stephanflug/digitales-Flugbuch/3D Druckerteile/Version 1 Basic mit Zero/DeckelV2.jpg

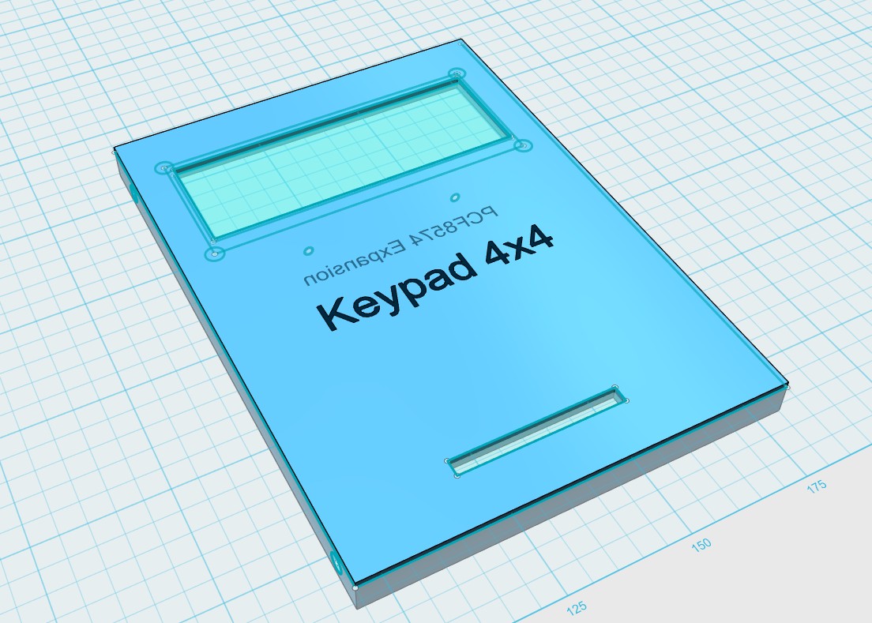
3D Druckerteile/Version 1 Basic mit Zero/DeckelV2.jpg
