stephanflug/digitales-Flugbuch/3D Druckerteile/Version 1 Basic mit Zero/GehäuseV2.jpg

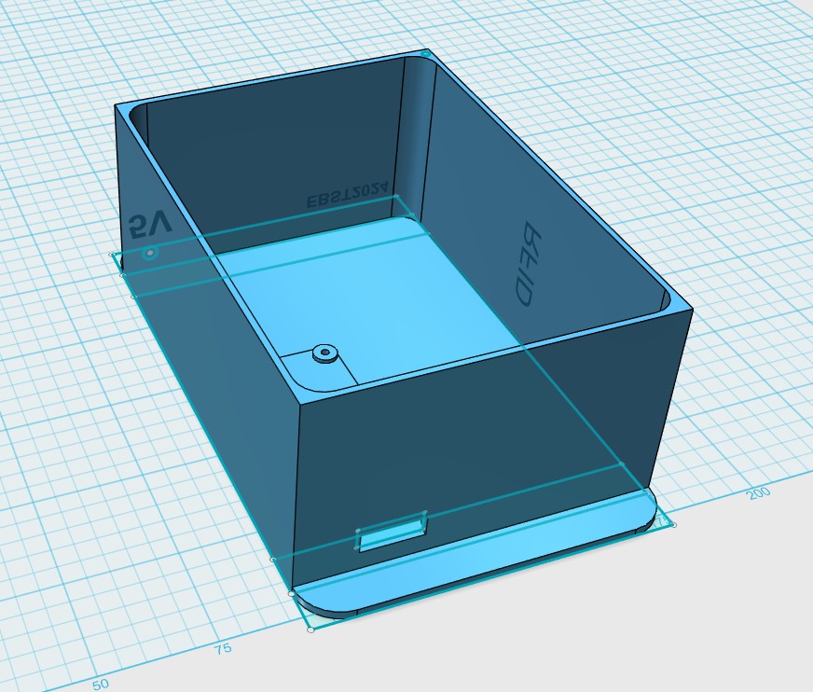
3D Druckerteile/Version 1 Basic mit Zero/GehäuseV2.jpg
