stephanflug/digitales-Flugbuch/3D Druckerteile/Version 2 Standard mit Zero/DigiFlugbuch Bild3.png

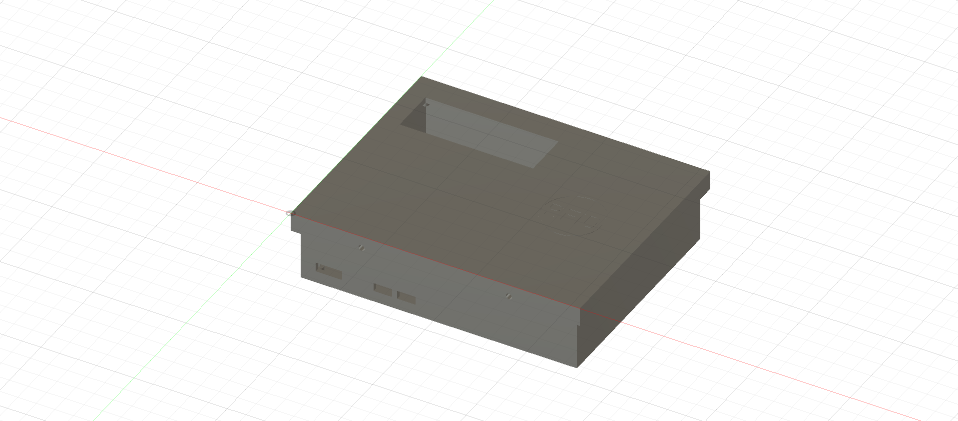
3D Druckerteile/Version 2 Standard mit Zero/DigiFlugbuch Bild3.png
