stephanflug/digitales-Flugbuch/3D Druckerteile/Version 2 Standard mit Zero/DigiFlugbuch Bild4.png

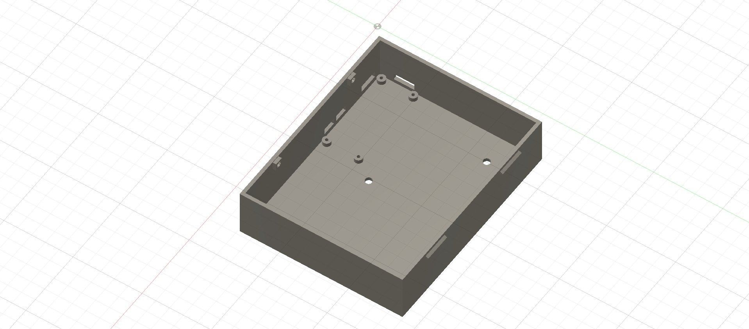
3D Druckerteile/Version 2 Standard mit Zero/DigiFlugbuch Bild4.png
