stephanflug/digitales-Flugbuch/3D Druckerteile/Version 4 Deluxe mit PI5/Fotos/IMG_7076.JPG

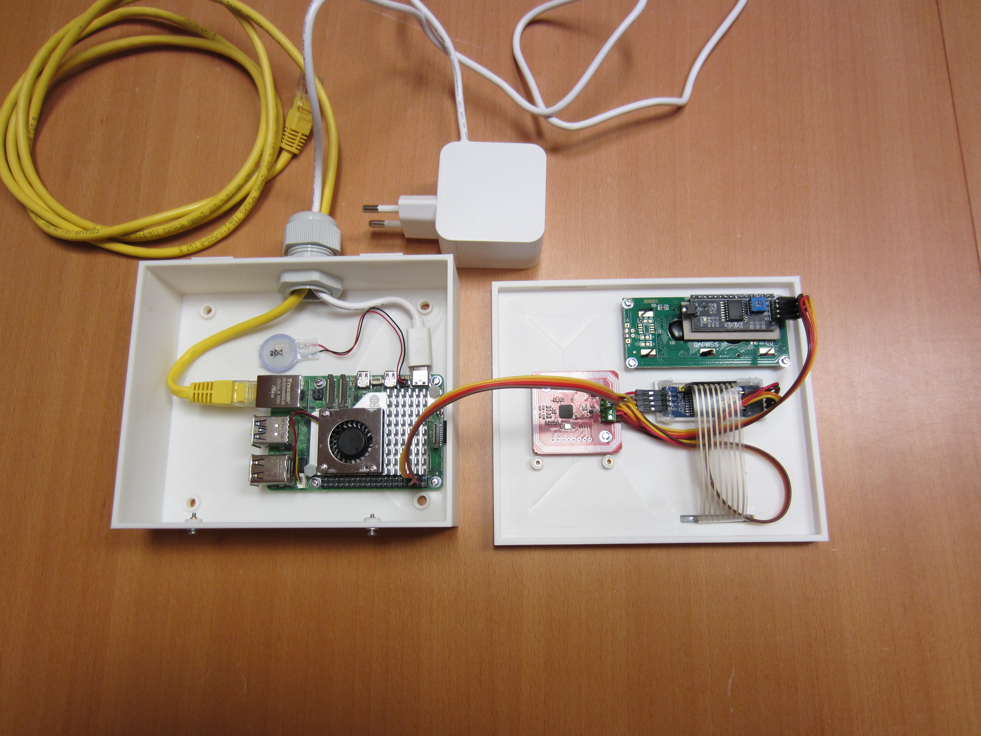
3D Druckerteile/Version 4 Deluxe mit PI5/Fotos/IMG_7076.JPG
