stephanflug/digitales-Flugbuch/3D Druckerteile/Zubehör/Wandhalterung/IMG_5251.jpeg

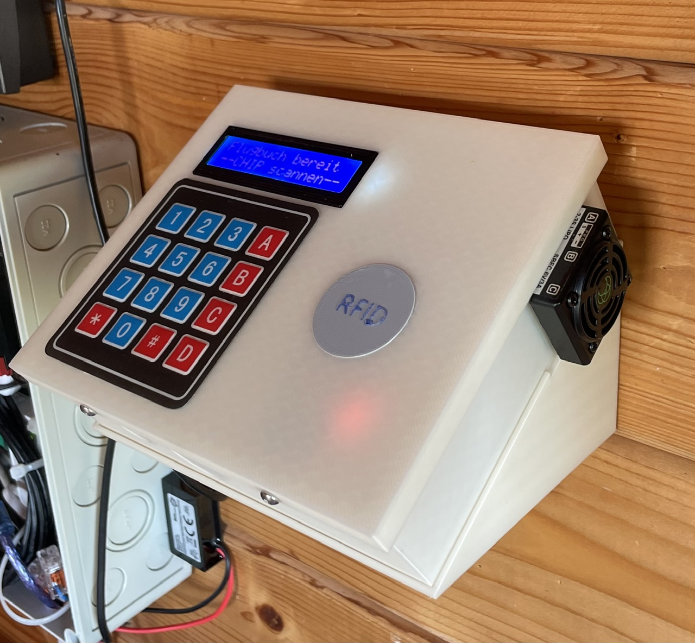
3D Druckerteile/Zubehör/Wandhalterung/IMG_5251.jpeg
