stephanflug/digitales-Flugbuch/Bilder/Bild 1.png

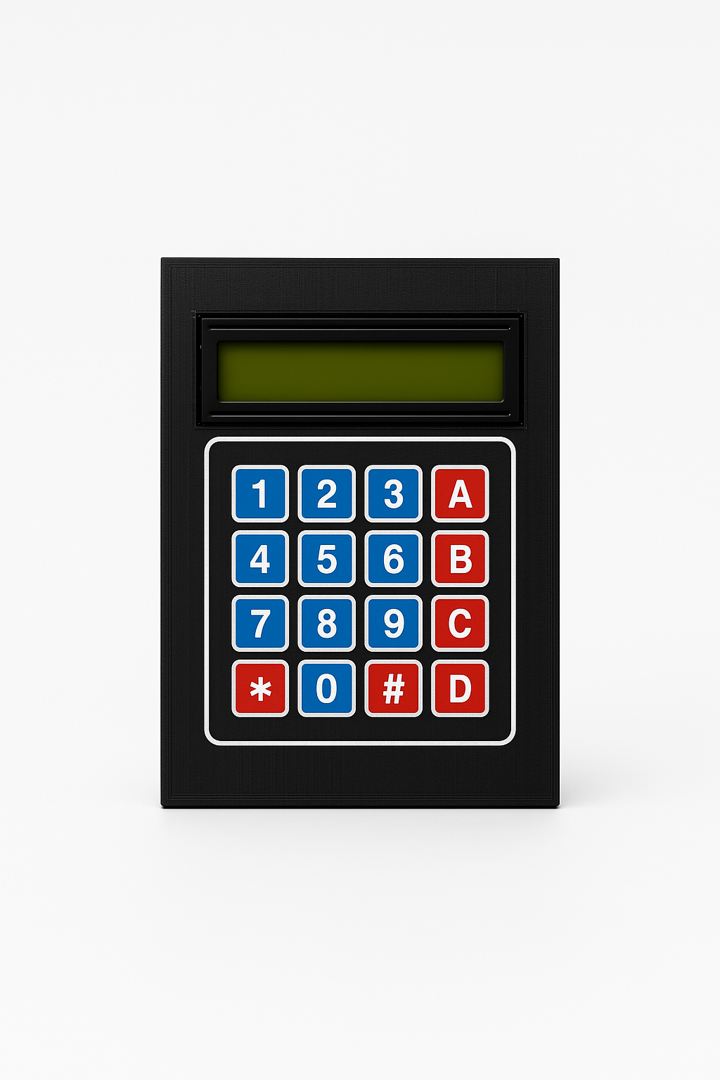
Bilder/Bild 1.png
