stephanflug/digitales-Flugbuch/Bilder/IMG_0768.JPG

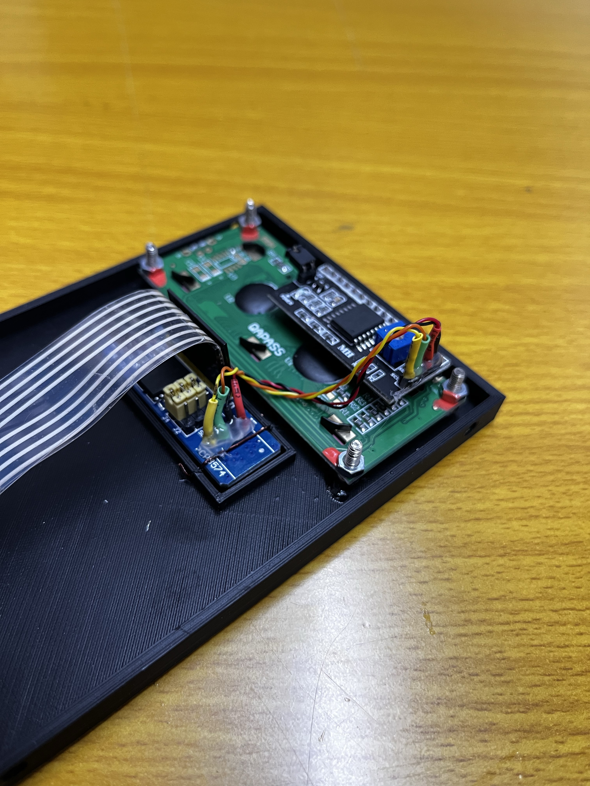
Bilder/IMG_0768.JPG
