stephanflug/digitales-Flugbuch/Bilder/Webbedienung/Ausgabe in json.jpg

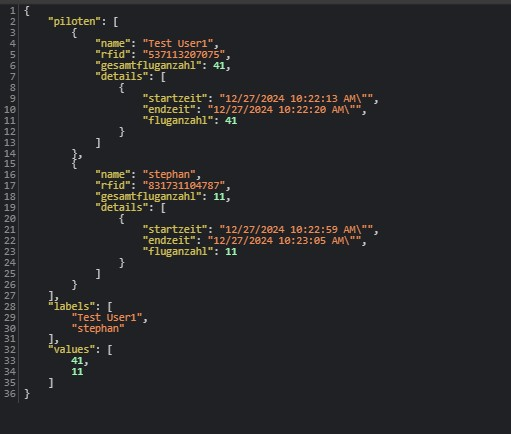
Bilder/Webbedienung/Ausgabe in json.jpg
