stephanflug/digitales-Flugbuch/Bilder/Webbedienung/Flugbuch Auswertung.jpg

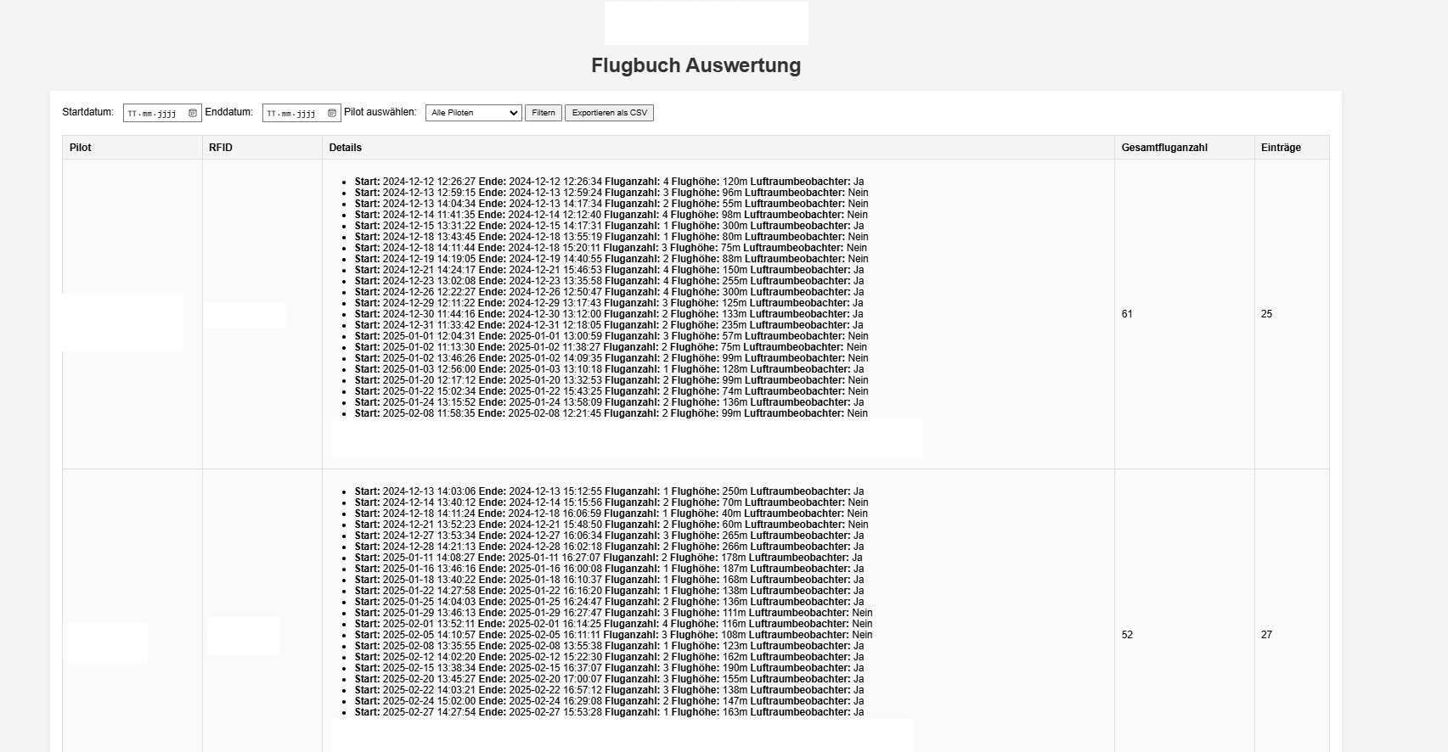
Bilder/Webbedienung/Flugbuch Auswertung.jpg
