stephanflug/digitales-Flugbuch/Bilder/Webbedienung/Flugbuch bearbeiten.jpg

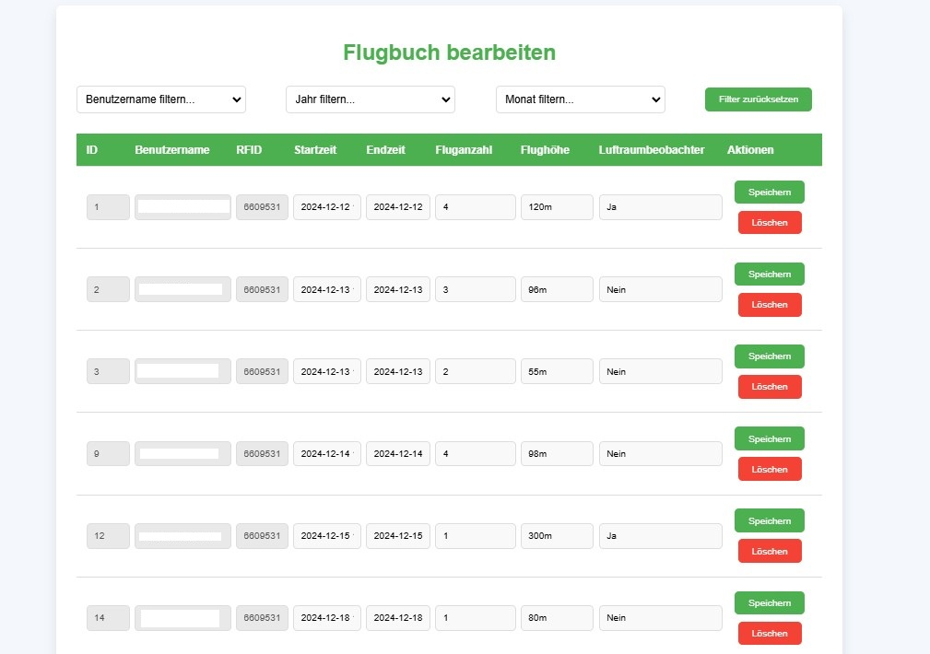
Bilder/Webbedienung/Flugbuch bearbeiten.jpg
