stephanflug/digitales-Flugbuch/Bilder/Webbedienung/Flugbuch Löschen.jpg

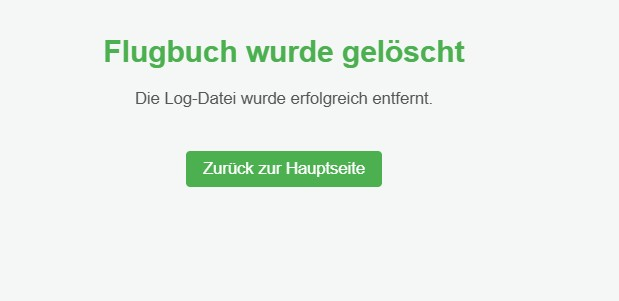
Bilder/Webbedienung/Flugbuch Löschen.jpg
