stephanflug/digitales-Flugbuch/Bilder/Webbedienung/SMTP Server.jpg

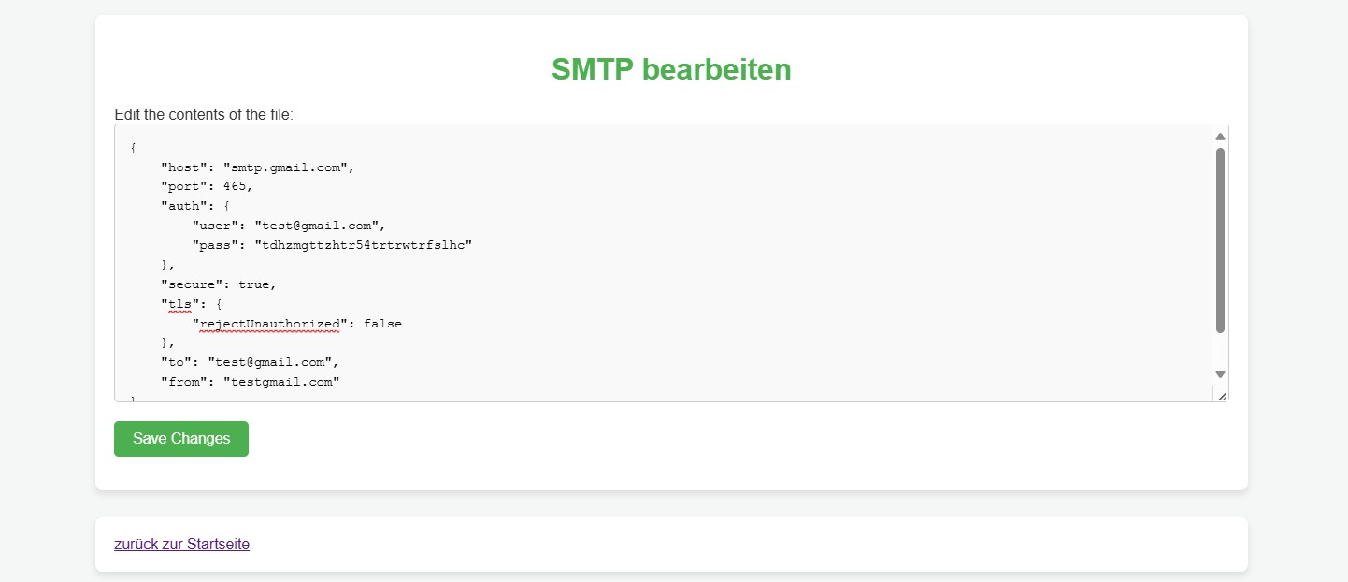
Bilder/Webbedienung/SMTP Server.jpg
