stephanflug/digitales-Flugbuch/BossServer/V1/Bilder/Flugdaten Auswertung export PDF.jpg

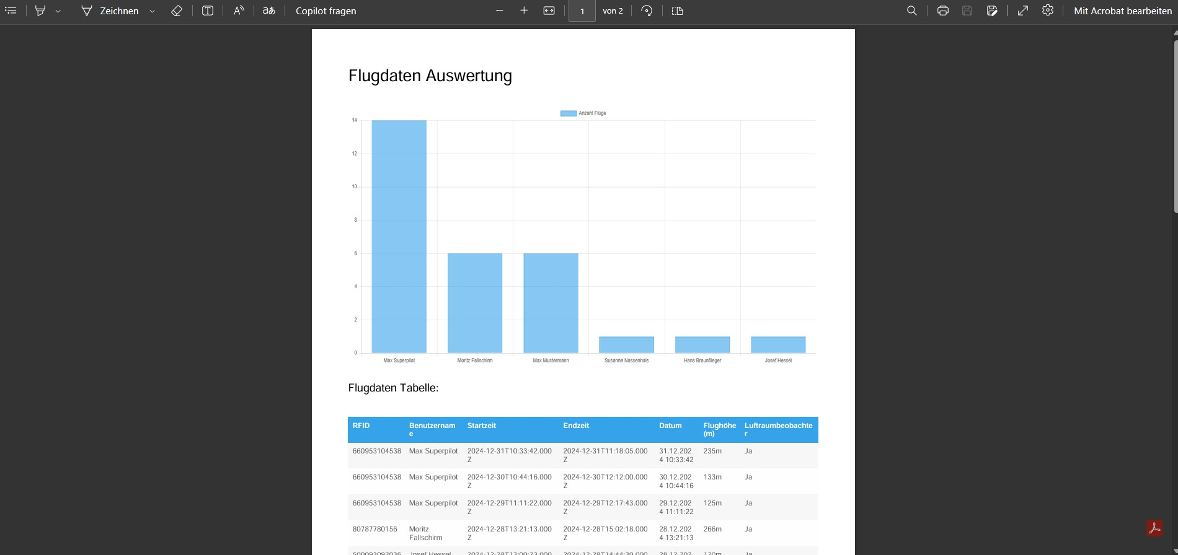
BossServer/V1/Bilder/Flugdaten Auswertung export PDF.jpg
