stephanflug/digitales-Flugbuch/BossServer/V1/Bilder/Login.jpg

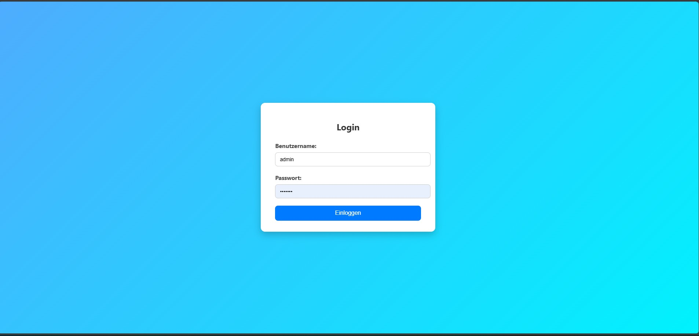
BossServer/V1/Bilder/Login.jpg
