stephanflug/digitales-Flugbuch/Tool Software/RFID Chip Scanner/PN532 Windows/Amazon DTECH FTDI USB zu TTL Seriell Adapter.png

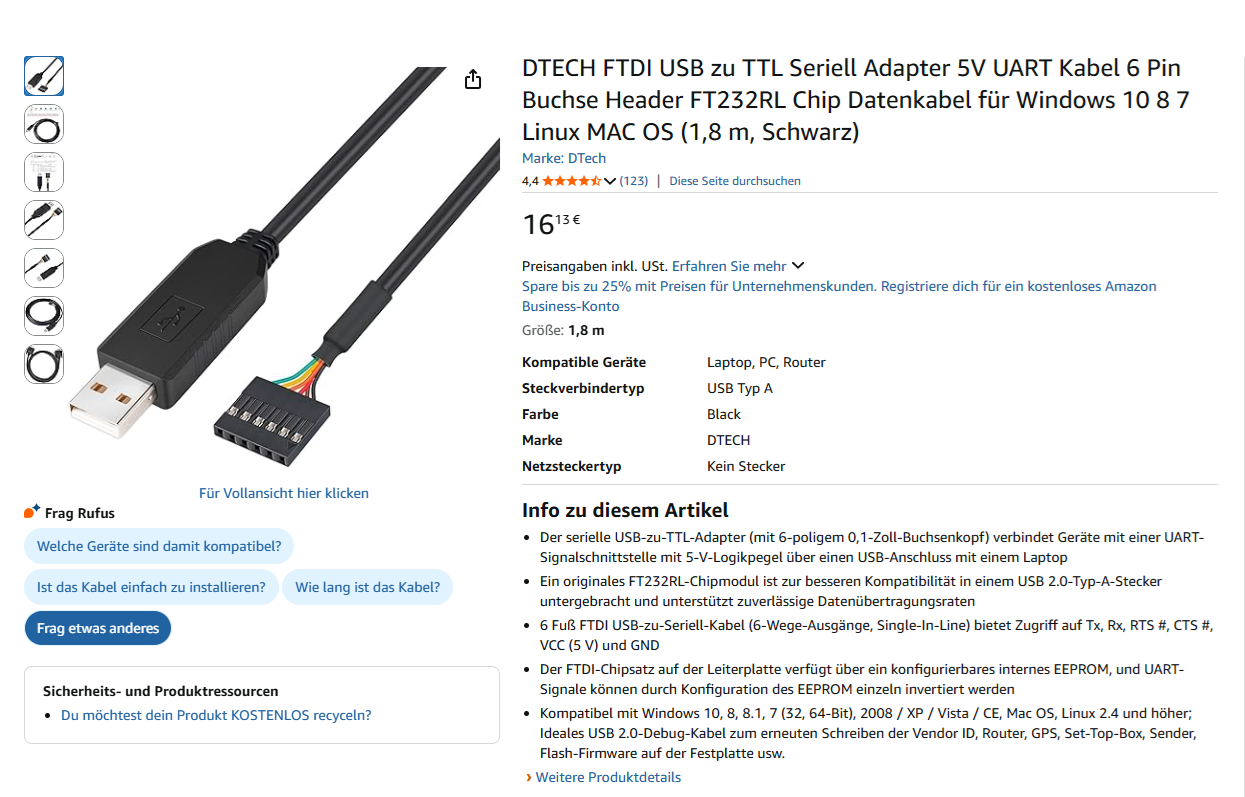
Tool Software/RFID Chip Scanner/PN532 Windows/Amazon DTECH FTDI USB zu TTL Seriell Adapter.png
