stephanflug/digitales-Flugbuch/Tool Software/RFID Chip Scanner/PN532 Windows/FTDI.png

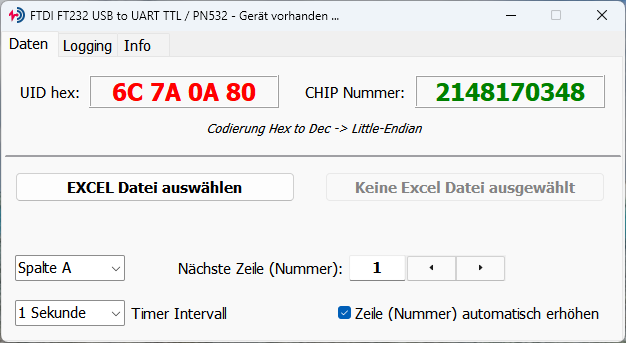
Tool Software/RFID Chip Scanner/PN532 Windows/FTDI.png
