stephanflug/digitales-Flugbuch/Tool Software/RFID Chip Scanner/PN532 Windows/IMG_20251127_120428.jpg

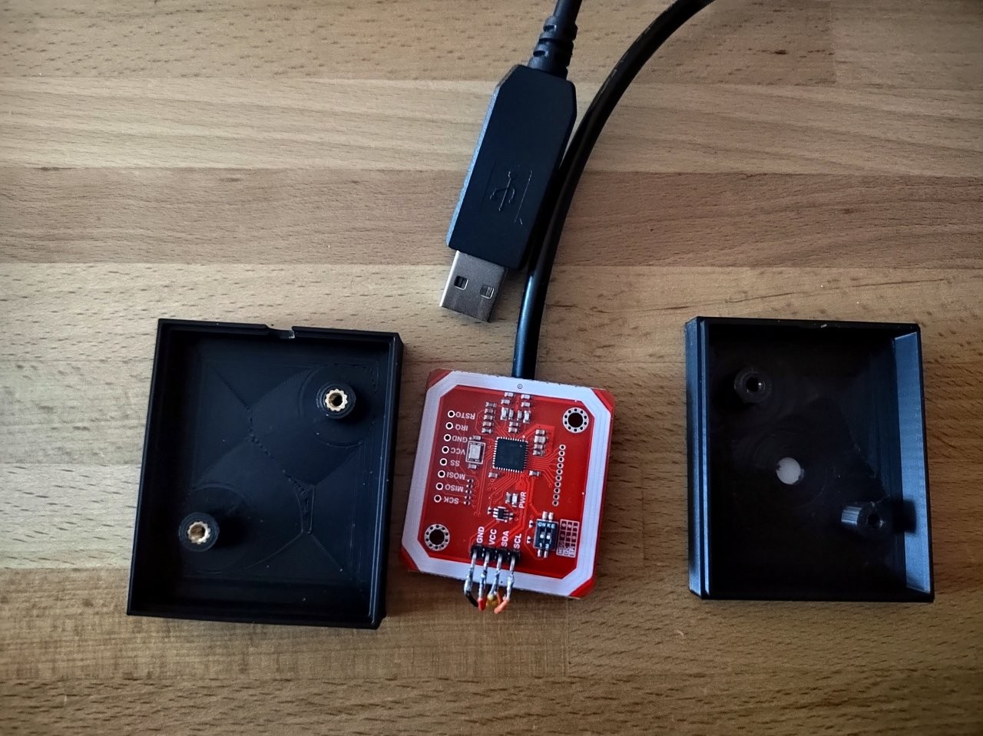
Tool Software/RFID Chip Scanner/PN532 Windows/IMG_20251127_120428.jpg
