stephanflug/digitales-Flugbuch/3D Druckerteile/Version 4 Deluxe mit PI5/Deckel_1_mit_Logo.stl

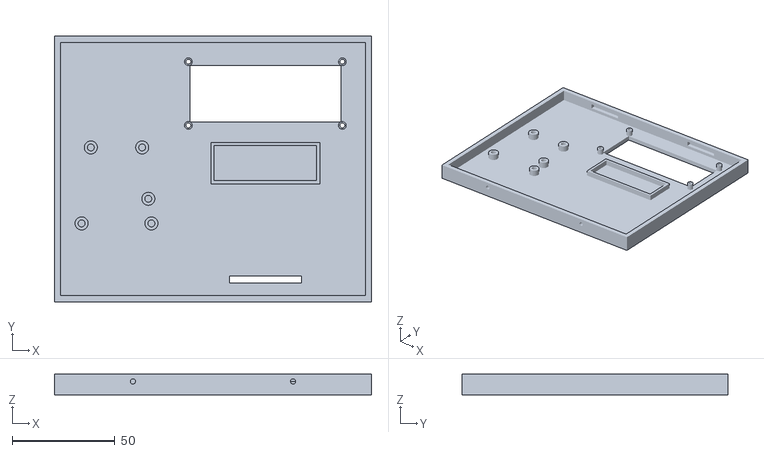
[picture p56: CAD file, 2025-10-23]
3D Druckerteile/Version 4 Deluxe mit PI5/Deckel_1_mit_Logo.stl
154.4 x 129.4 x 10.00
