stephanflug/digitales-Flugbuch/Tool Software/RFID Chip Scanner/PN532 Windows/3D FTDI Oben.stl

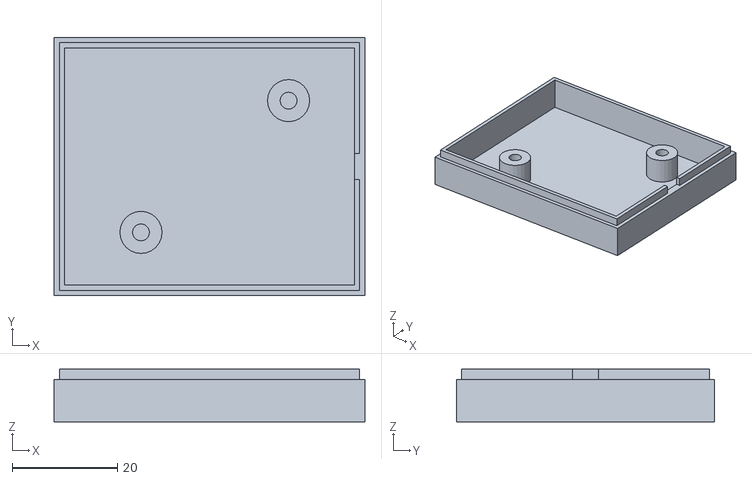
[picture p57: CAD file, 2025-11-27]
Tool Software/RFID Chip Scanner/PN532 Windows/3D FTDI Oben.stl
59.0 x 49.0 x 10.0
