stephanflug/digitales-Flugbuch/Tool Software/RFID Chip Scanner/PN532 Windows/3D FTDI Fenster.stl

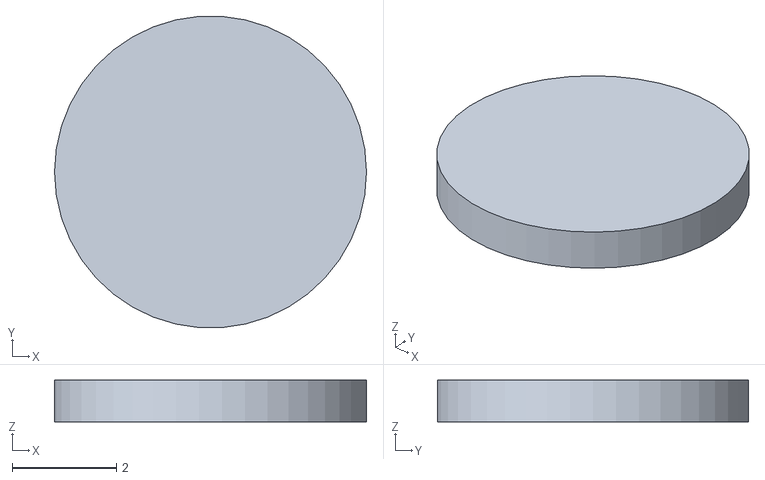
[picture p58: CAD file, 2025-11-27]
Tool Software/RFID Chip Scanner/PN532 Windows/3D FTDI Fenster.stl
6.00 x 5.98 x 0.8
