stephanflug/digitales-Flugbuch/3D Druckerteile/Version 4 Deluxe mit PI5/Gehäuse_PG16_unten.stl

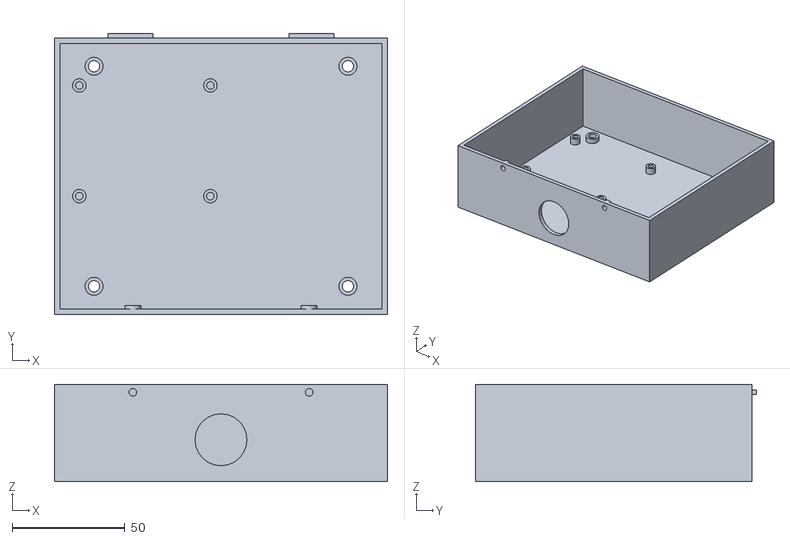
[picture p60: CAD file, 2025-10-23]
3D Druckerteile/Version 4 Deluxe mit PI5/Gehäuse_PG16_unten.stl
147.4 x 124.4 x 43.0
