stephanflug/digitales-Flugbuch/Bilder/IMG_0760.JPG

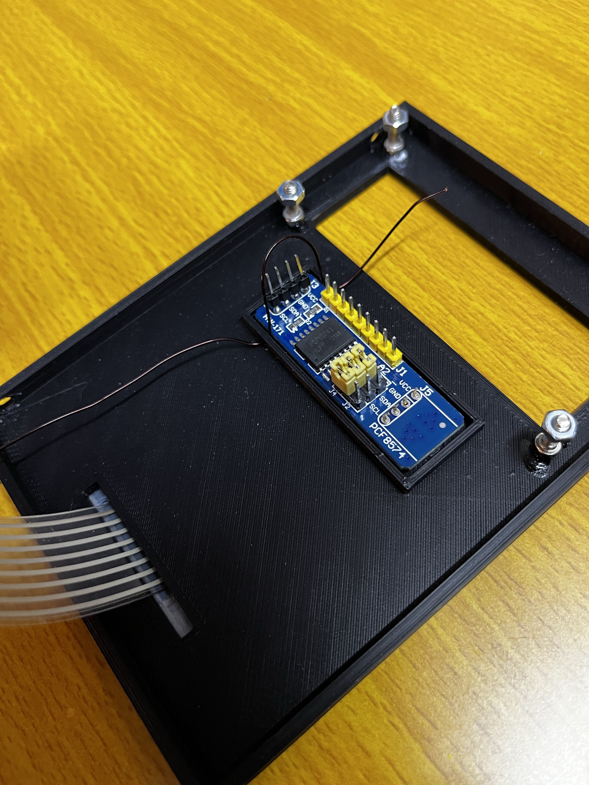
Bilder/IMG_0760.JPG
