stephanflug/digitales-Flugbuch/Bilder/IMG_0763.JPG

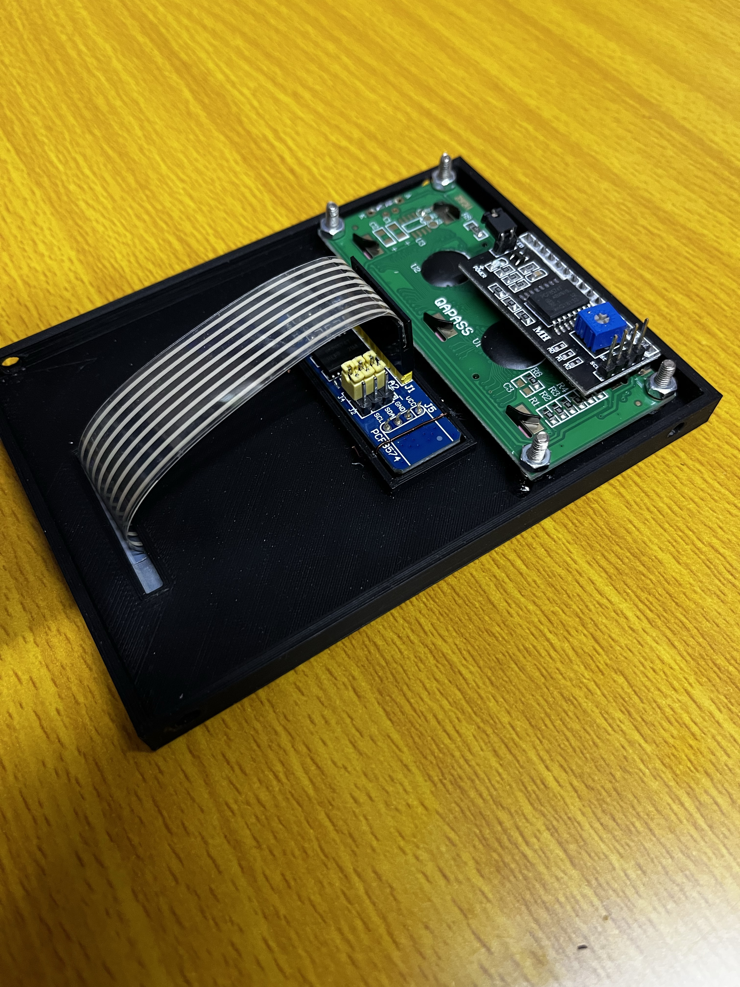
Bilder/IMG_0763.JPG
